GMUCERG/fobos/docs/source/examples/index.rst

****
Example Jupyter Notebooks
****

  * Correlation Power Analysis with FOBOS Shield
  * Correlation Power Analysis with Picoscope
  * Test Vector Leakage Assessment with FOBOS Shield
