GMUCERG/fobos/docs/source/modules/index.rst

.. _modules-label:

*************
FOBOS Modules
*************
FOBOS supports two boards for FOBOS Control:

#. Digilent Pynq-Z1
#. TUL Pynq-Z2

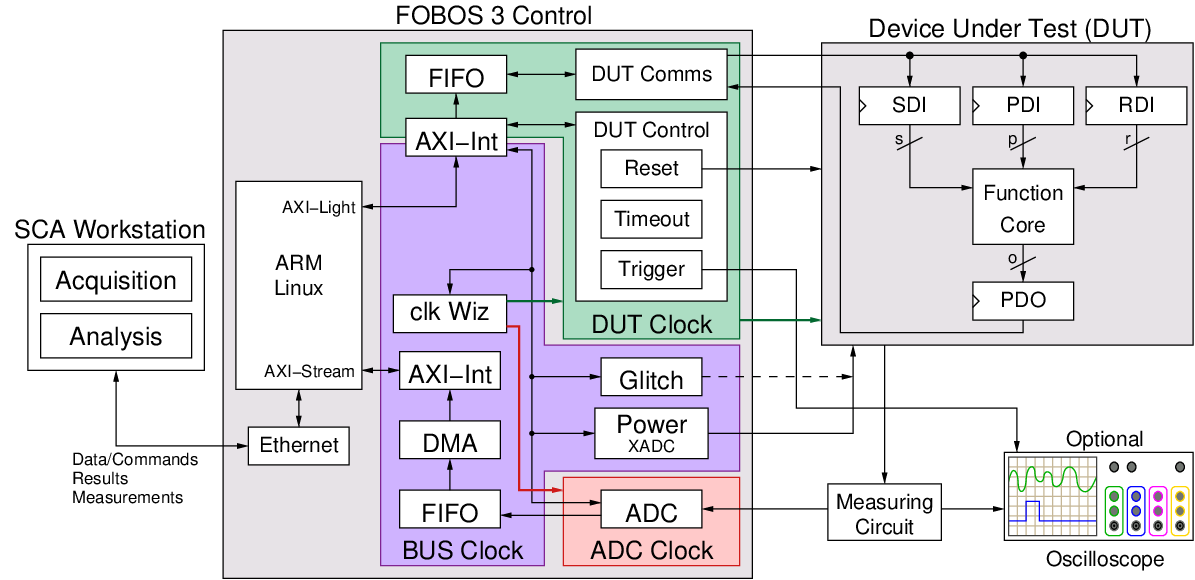
[picture p10: docs/source/figures/fobos3-block.png]


   Block Diagram of FOBOS with Pynq-Z1/Z2 as control board

Here is a list of the available modules:

- :ref:`dut_comms-label` including *DUT Interface*, *Output Length*
- :ref:`dut_control-label` including *DUT Clock*, *DUT Selection*, *Trigger*, *Reset*, *Timeout*, *Glitch*  and *DUT Working Counter*
- :ref:`openADC-label` (requires FOBOS Shield)
- :ref:`power-label` (requires FOBOS Shield)

.. toctree::
   :hidden:
   
   dut_comms
   dut_control
   openadc
   power
