GMUCERG/fobos/docs/source/teaching/index.rst

****
Class Projects
****

    * Project 1: Correlation Power Analysis (CPA) - Data Acquisition
    * Project 2: Correlation Power Analysis (CPA) - Data Analysis
    * Project 3: Side-Channel Leakage Assessment
