GMUCERG/fobos/docs/source/figures/pmod_basys3.pdf

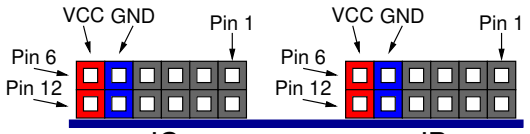
[picture p11: figure]
Pin 12; Pin 6; VCC GND; Pin 1

JC | JB
JA | JXADC
