GMUCERG/fobos/docs/source/figures/lwc/interface.pdf

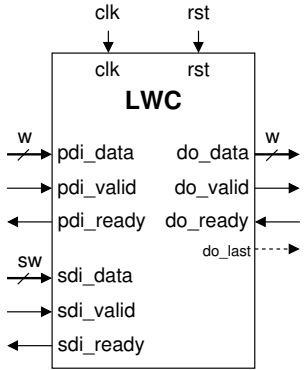
[picture p16: figure]
clk; rst; LWC; pdi_valid; pdi_ready; do_ready; do_valid; sdi_valid; sdi_ready; sdi_data; pdi_data; do_data; do_last

### Public Data Input Ports

### PDI

### Secret Data Input Ports

### SDI

### Data Output Ports

DO
