GMUCERG/fobos/docs/source/figures/lwc/interface_sca.pdf

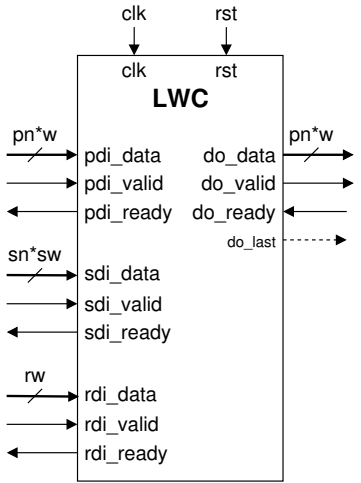
[picture p17: figure]
LWC; rdi_data; sdi_data; sdi_valid; sdi_ready; pdi_ready; pdi_valid; pdi_data; rdi_valid; rdi_ready; do_data; do_valid; do_ready; do_last; clk; rst

### PDI Public Data Input Ports

### SDI Secret Data Input Ports

### RDI Random Data Input Ports

### Data Output Ports

DO
