GMUCERG/fobos/control/pynqctrl/figures/pynq-modifications-shield-rev1.jpg

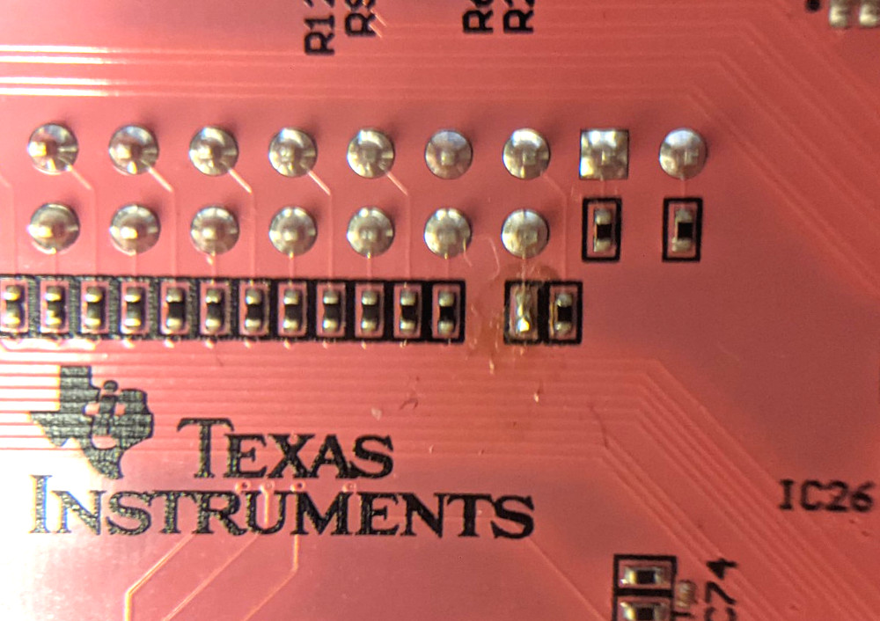
control/pynqctrl/figures/pynq-modifications-shield-rev1.jpg
