GMUCERG/fobos/control/pynqctrl/figures/resistor-R76.jpg

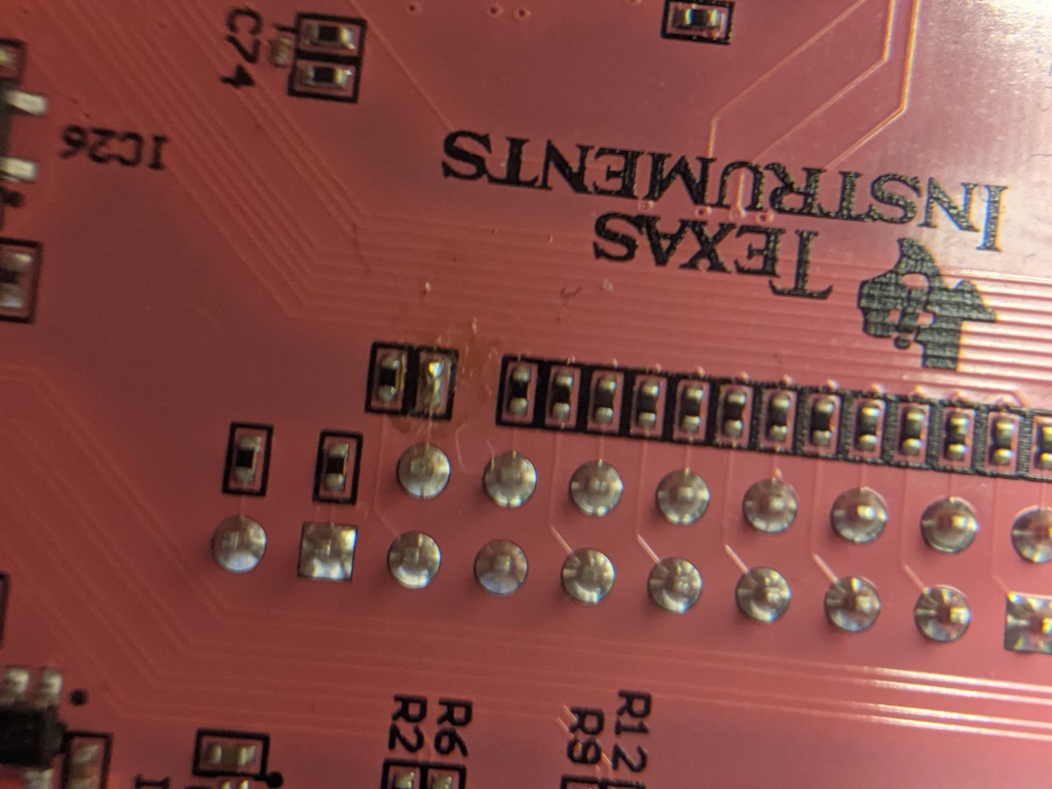
control/pynqctrl/figures/resistor-R76.jpg
