GMUCERG/fobos/docs/source/cergimg/cerg.png

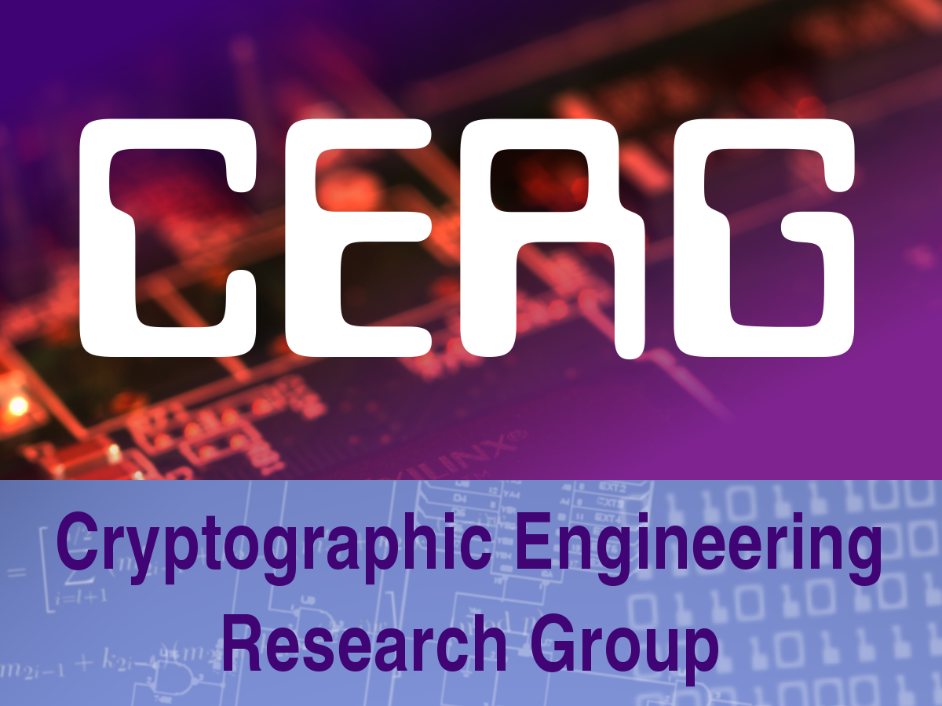
docs/source/cergimg/cerg.png
