GMUCERG/fobos/docs/source/figures/FOBOS3-Artix7-A12.jpg

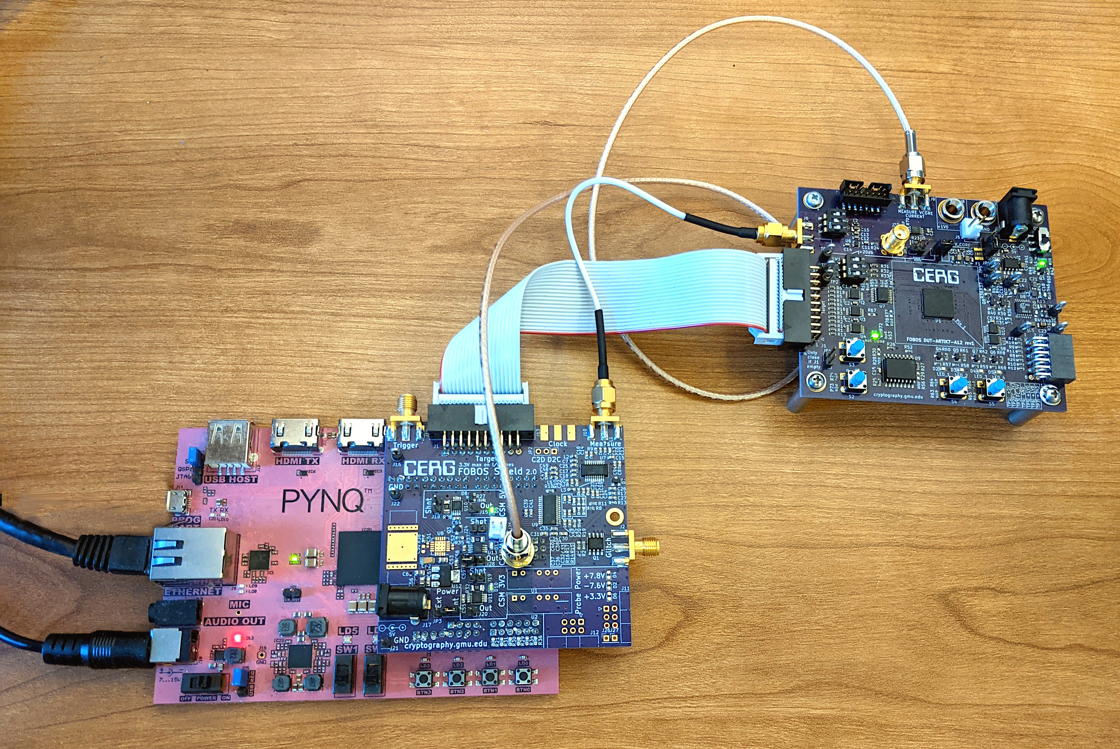
docs/source/figures/FOBOS3-Artix7-A12.jpg
