GMUCERG/fobos/docs/source/figures/FOBOS_MTC.jpg

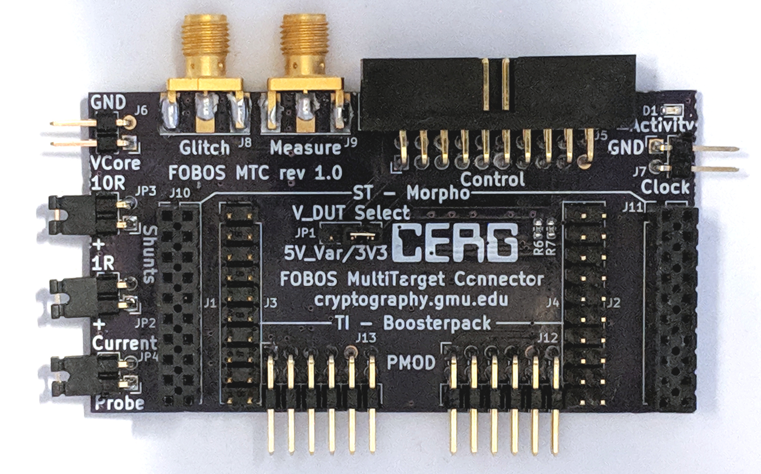
docs/source/figures/FOBOS_MTC.jpg
