GMUCERG/fobos/docs/source/figures/pmod_basys3.png

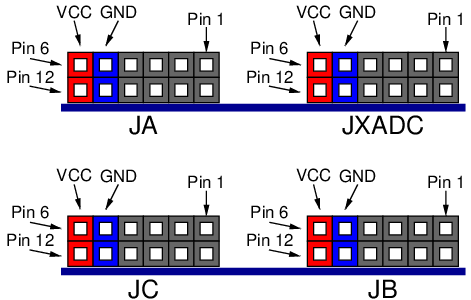
docs/source/figures/pmod_basys3.png
