GMUCERG/fobos/docs/source/figures/pmod_pynq.png

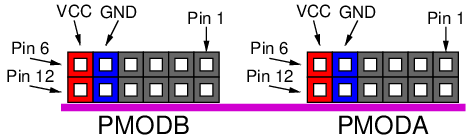
docs/source/figures/pmod_pynq.png
