GMUCERG/fobos/docs/source/figures/Pynq-Z2-modifications2.jpg

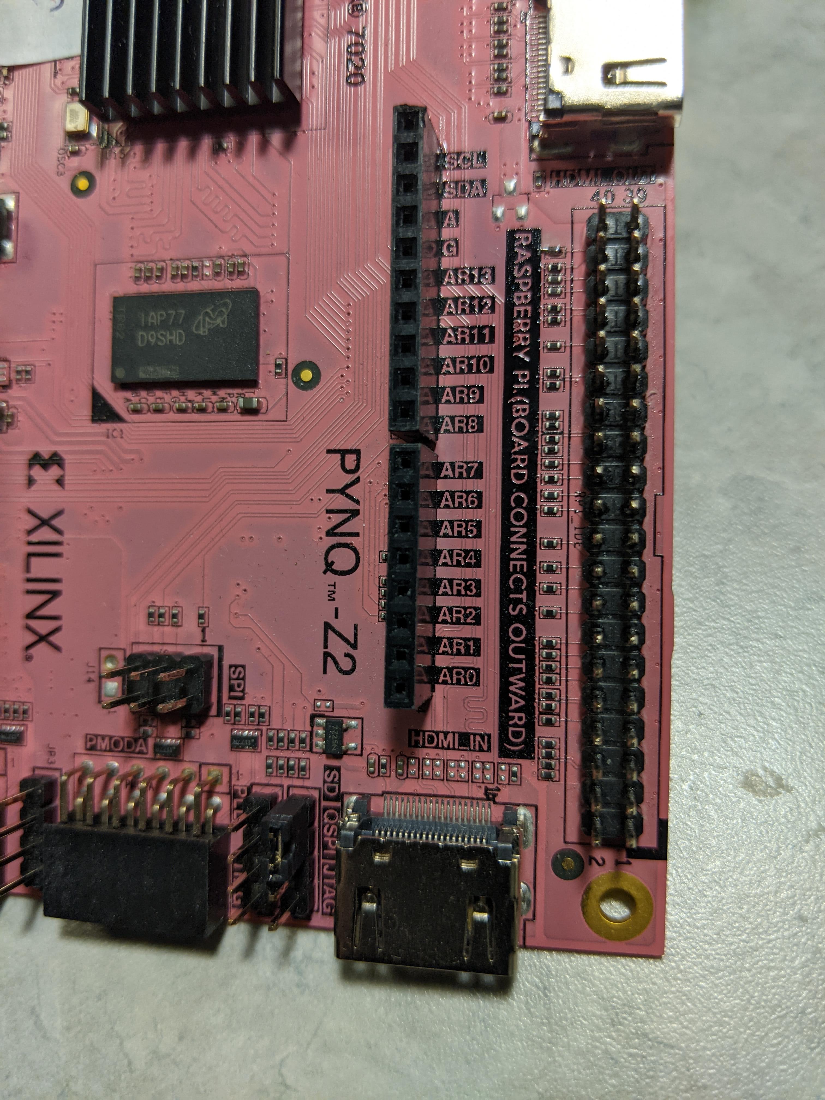
docs/source/figures/Pynq-Z2-modifications2.jpg
