GMUCERG/fobos/docs/source/figures/Pynq-Z2_with-FBD-A7.jpg

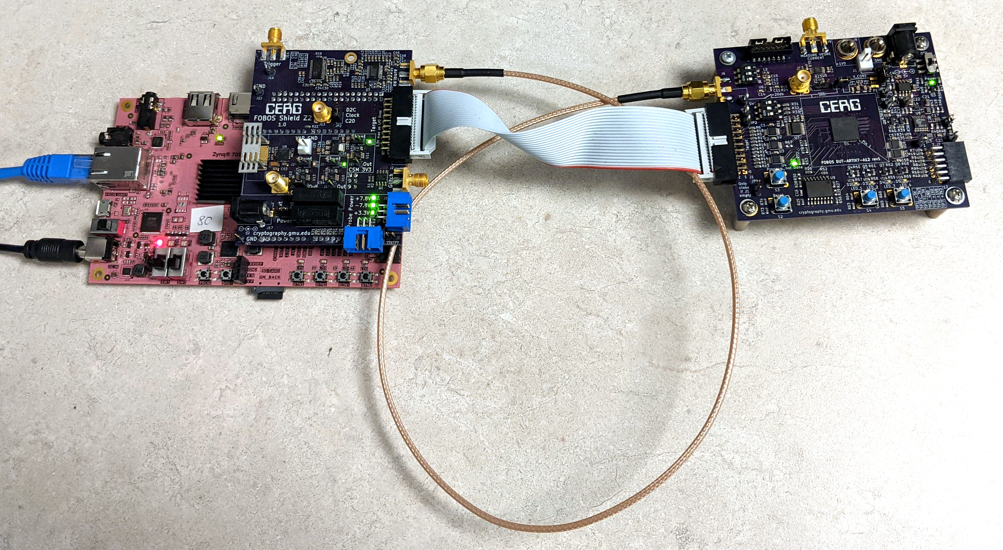
docs/source/figures/Pynq-Z2_with-FBD-A7.jpg
