GMUCERG/fobos/hardware/fobos-dut/dut-artix7-a12t-cpg238/cerg_3d_models/User Library-SSOP16.step

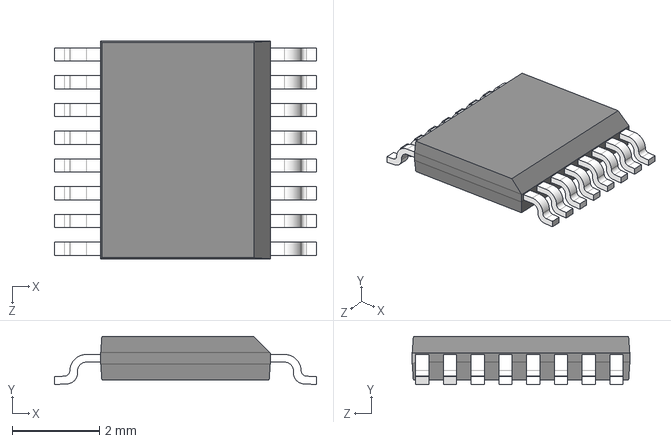
[picture p41: CAD file, 2023-11-30]
hardware/fobos-dut/dut-artix7-a12t-cpg238/cerg_3d_models/User Library-SSOP16.step
5.99 x 1.10 x 4.98 mm
