GMUCERG/fobos/hardware/fobos-dut/dut-artix7-a12t-cpg238/3d models/keystone-PN5281.STEP

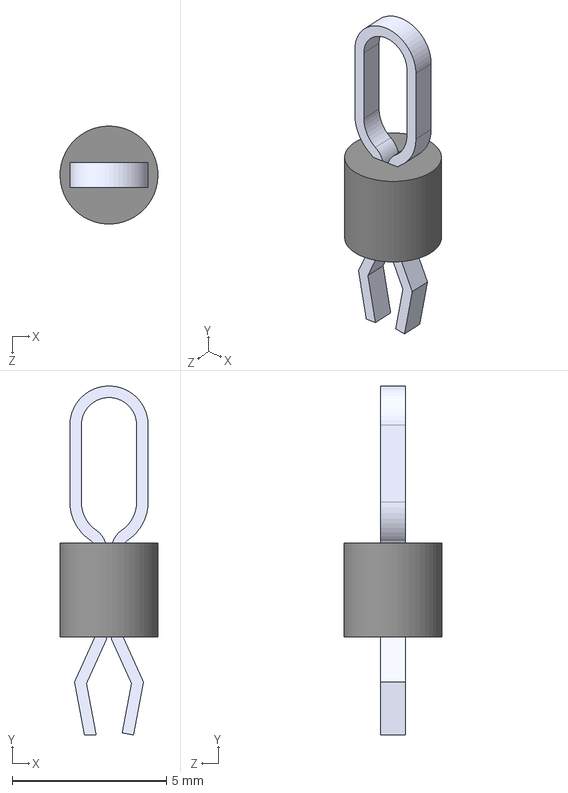
[picture p42: CAD file, 2023-11-30]
hardware/fobos-dut/dut-artix7-a12t-cpg238/3d models/keystone-PN5281.STEP
3.17 x 11.3 x 3.17 mm
