GMUCERG/fobos/hardware/fobos-dut/dut-artix7-a12t-cpg238/3d models/BRC2012T3R3MD.STEP

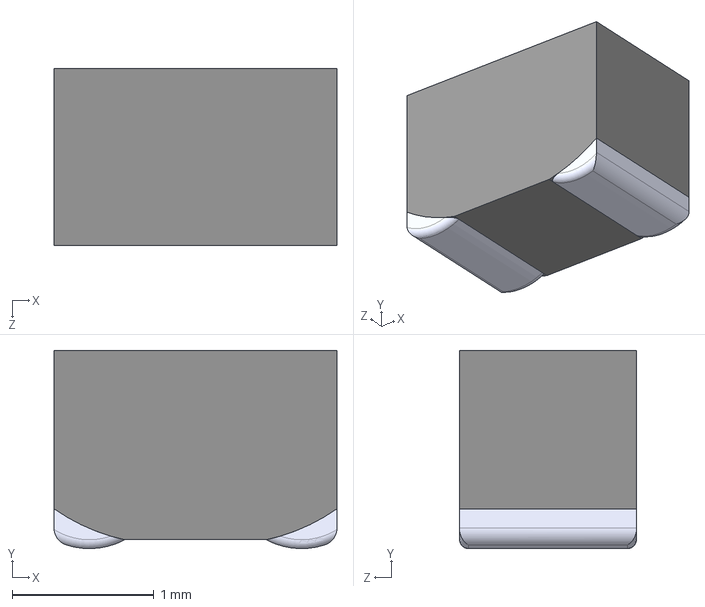
[picture p43: CAD file, 2023-11-30]
hardware/fobos-dut/dut-artix7-a12t-cpg238/3d models/BRC2012T3R3MD.STEP
2.00 x 1.40 x 1.25 mm
