GMUCERG/fobos/hardware/fobos-dut/dut-artix7-a12t-cpg238/3d models/keystone-PN575-8.STEP

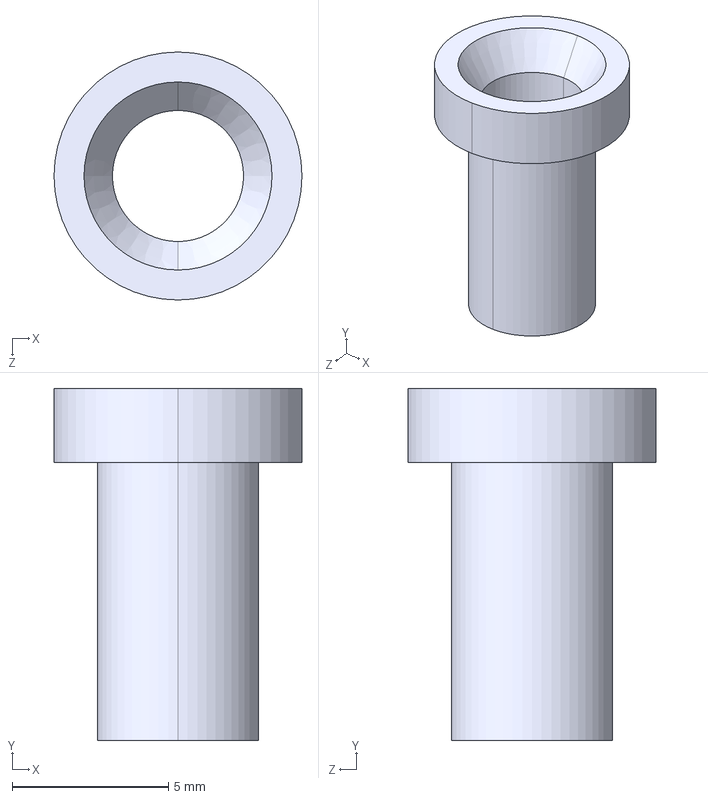
[picture p44: CAD file, 2023-11-30]
hardware/fobos-dut/dut-artix7-a12t-cpg238/3d models/keystone-PN575-8.STEP
7.92 x 11.3 x 7.92 mm
