GMUCERG/fobos/hardware/fobos-dut/dut-artix7-a12t-cpg238/3d models/XA7A25T-1CPG238Q.stp

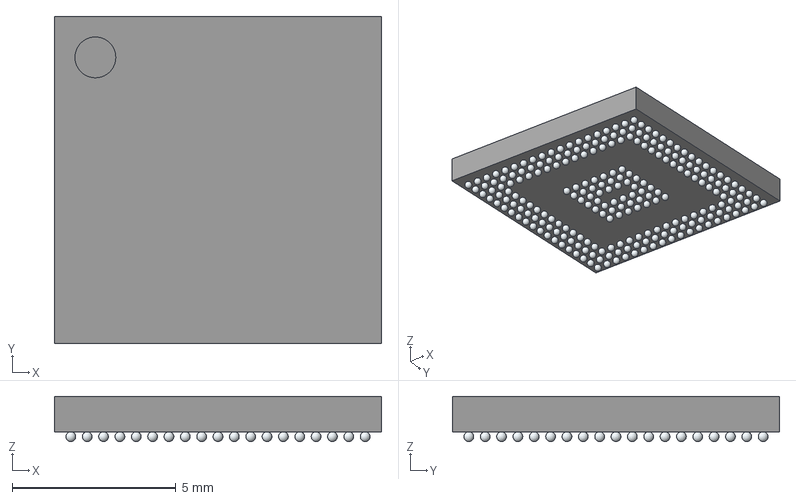
[picture p45: CAD file, 2023-11-30]
hardware/fobos-dut/dut-artix7-a12t-cpg238/3d models/XA7A25T-1CPG238Q.stp
10.0 x 10.0 x 1.38 mm
A1
A2
A3
A4
A5
A6
A7
A8
A9
A10
A11
A12
A13
A14
A15
A16
A17
A18
A19
B1
B2
B3
B4
B5
B6
B7
B8
B9
B10
B11
B12
B13
B14
B15
B16
B17
B18
B19
C1
C2
C3
C4
C5
C6
C7
C8
C9
C10
C11
C12
C13
C14
C15
C16
C17
C18
C19
D1
D2
D3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
