GMUCERG/fobos/software/notebooks/sca_labs/figures/FOBOS3-lab-setup.jpg

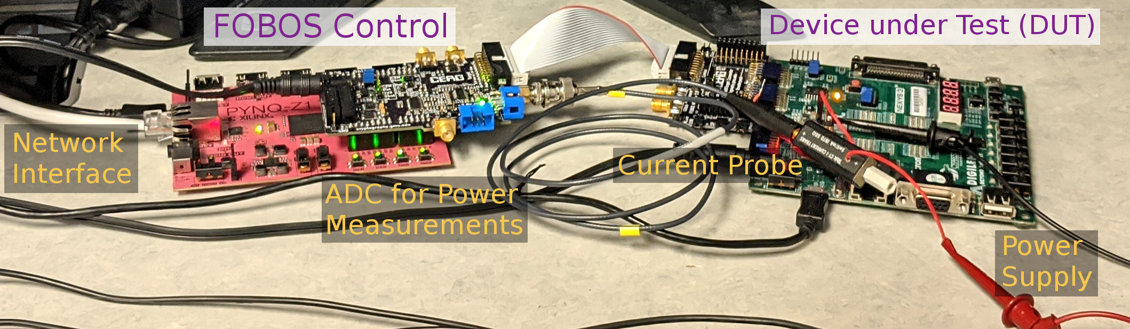
software/notebooks/sca_labs/figures/FOBOS3-lab-setup.jpg
