GMUCERG/fobos/control/ip_repo/dut_controller_1.0/drivers/dut_controller_v1_0/src/dut_controller.h

#ifndef DUT_CONTROLLER_H
#define DUT_CONTROLLER_H


/****************** Include Files ********************/
#include "xil_types.h"
#include "xstatus.h"

#define DUT_CONTROLLER_S_AXI_SLV_REG0_OFFSET 0
#define DUT_CONTROLLER_S_AXI_SLV_REG1_OFFSET 4
#define DUT_CONTROLLER_S_AXI_SLV_REG2_OFFSET 8
#define DUT_CONTROLLER_S_AXI_SLV_REG3_OFFSET 12
#define DUT_CONTROLLER_S_AXI_SLV_REG4_OFFSET 16
#define DUT_CONTROLLER_S_AXI_SLV_REG5_OFFSET 20
#define DUT_CONTROLLER_S_AXI_SLV_REG6_OFFSET 24
#define DUT_CONTROLLER_S_AXI_SLV_REG7_OFFSET 28


/**************************** Type Definitions *****************************/
/**
 *
 * Write a value to a DUT_CONTROLLER register. A 32 bit write is performed.
 * If the component is implemented in a smaller width, only the least
 * significant data is written.
 *
 * @param   BaseAddress is the base address of the DUT_CONTROLLERdevice.
 * @param   RegOffset is the register offset from the base to write to.
 * @param   Data is the data written to the register.
 *
 * @return  None.
 *
 * @note
 * C-style signature:
 * 	void DUT_CONTROLLER_mWriteReg(u32 BaseAddress, unsigned RegOffset, u32 Data)
 *
 */
#define DUT_CONTROLLER_mWriteReg(BaseAddress, RegOffset, Data) \
  	Xil_Out32((BaseAddress) + (RegOffset), (u32)(Data))

/**
 *
 * Read a value from a DUT_CONTROLLER register. A 32 bit read is performed.
 * If the component is implemented in a smaller width, only the least
 * significant data is read from the register. The most significant data
 * will be read as 0.
 *
 * @param   BaseAddress is the base address of the DUT_CONTROLLER device.
 * @param   RegOffset is the register offset from the base to write to.
 *
 * @return  Data is the data from the register.
 *
 * @note
 * C-style signature:
 * 	u32 DUT_CONTROLLER_mReadReg(u32 BaseAddress, unsigned RegOffset)
 *
 */
#define DUT_CONTROLLER_mReadReg(BaseAddress, RegOffset) \
    Xil_In32((BaseAddress) + (RegOffset))

/************************** Function Prototypes ****************************/
/**
 *
 * Run a self-test on the driver/device. Note this may be a destructive test if
 * resets of the device are performed.
 *
 * If the hardware system is not built correctly, this function may never
 * return to the caller.
 *
 * @param   baseaddr_p is the base address of the DUT_CONTROLLER instance to be worked on.
 *
 * @return
 *
 *    - XST_SUCCESS   if all self-test code passed
 *    - XST_FAILURE   if any self-test code failed
 *
 * @note    Caching must be turned off for this function to work.
 * @note    Self test may fail if data memory and device are not on the same bus.
 *
 */
XStatus DUT_CONTROLLER_Reg_SelfTest(void * baseaddr_p);

#endif // DUT_CONTROLLER_H
