GMUCERG/fobos/control/ip_repo/powermanager_1.1/src/xadc_wiz_0/xadc_wiz_0.vhd

-- file: xadc_wiz_0.vhd
-- (c) Copyright 2009 - 2013 Xilinx, Inc. All rights reserved.
-- 
-- This file contains confidential and proprietary information
-- of Xilinx, Inc. and is protected under U.S. and
-- international copyright and other intellectual property
-- laws.
-- 
-- DISCLAIMER
-- This disclaimer is not a license and does not grant any
-- rights to the materials distributed herewith. Except as
-- otherwise provided in a valid license issued to you by
-- Xilinx, and to the maximum extent permitted by applicable
-- law: (1) THESE MATERIALS ARE MADE AVAILABLE "AS IS" AND
-- WITH ALL FAULTS, AND XILINX HEREBY DISCLAIMS ALL WARRANTIES
-- AND CONDITIONS, EXPRESS, IMPLIED, OR STATUTORY, INCLUDING
-- BUT NOT LIMITED TO WARRANTIES OF MERCHANTABILITY, NON-
-- INFRINGEMENT, OR FITNESS FOR ANY PARTICULAR PURPOSE; and
-- (2) Xilinx shall not be liable (whether in contract or tort,
-- including negligence, or under any other theory of
-- liability) for any loss or damage of any kind or nature
-- related to, arising under or in connection with these
-- materials, including for any direct, or any indirect,
-- special, incidental, or consequential loss or damage
-- (including loss of data, profits, goodwill, or any type of
-- loss or damage suffered as a result of any action brought
-- by a third party) even if such damage or loss was
-- reasonably foreseeable or Xilinx had been advised of the
-- possibility of the same.
-- 
-- CRITICAL APPLICATIONS
-- Xilinx products are not designed or intended to be fail-
-- safe, or for use in any application requiring fail-safe
-- performance, such as life-support or safety devices or
-- systems, Class III medical devices, nuclear facilities,
-- applications related to the deployment of airbags, or any
-- other applications that could lead to death, personal
-- injury, or severe property or environmental damage
-- (individually and collectively, "Critical
-- Applications"). Customer assumes the sole risk and
-- liability of any use of Xilinx products in Critical
-- Applications, subject only to applicable laws and
-- regulations governing limitations on product liability.
-- 
-- THIS COPYRIGHT NOTICE AND DISCLAIMER MUST BE RETAINED AS
-- PART OF THIS FILE AT ALL TIMES.

library ieee;
use ieee.std_logic_1164.all;
use ieee.numeric_std.all;
Library UNISIM;
use UNISIM.VCOMPONENTS.ALL;

entity xadc_wiz_0 is
   port
   (
    daddr_in        : in  STD_LOGIC_VECTOR (6 downto 0);     -- Address bus for the dynamic reconfiguration port
    den_in          : in  STD_LOGIC;                         -- Enable Signal for the dynamic reconfiguration port
    di_in           : in  STD_LOGIC_VECTOR (15 downto 0);    -- Input data bus for the dynamic reconfiguration port
    dwe_in          : in  STD_LOGIC;                         -- Write Enable for the dynamic reconfiguration port
    do_out          : out  STD_LOGIC_VECTOR (15 downto 0);   -- Output data bus for dynamic reconfiguration port
    drdy_out        : out  STD_LOGIC;                        -- Data ready signal for the dynamic reconfiguration port
    dclk_in         : in  STD_LOGIC;                         -- Clock input for the dynamic reconfiguration port
    reset_in        : in  STD_LOGIC;                         -- Reset signal for the System Monitor control logic
    vauxp1          : in  STD_LOGIC;                         -- Auxiliary Channel 1
    vauxn1          : in  STD_LOGIC;
    vauxp5          : in  STD_LOGIC;                         -- Auxiliary Channel 5
    vauxn5          : in  STD_LOGIC;
    vauxp6          : in  STD_LOGIC;                         -- Auxiliary Channel 6
    vauxn6          : in  STD_LOGIC;
    vauxp9          : in  STD_LOGIC;                         -- Auxiliary Channel 9
    vauxn9          : in  STD_LOGIC;
    vauxp13         : in  STD_LOGIC;                         -- Auxiliary Channel 13
    vauxn13         : in  STD_LOGIC;
    vauxp15         : in  STD_LOGIC;                         -- Auxiliary Channel 15
    vauxn15         : in  STD_LOGIC;
    busy_out        : out  STD_LOGIC;                        -- ADC Busy signal
    channel_out     : out  STD_LOGIC_VECTOR (4 downto 0);    -- Channel Selection Outputs
    eoc_out         : out  STD_LOGIC;                        -- End of Conversion Signal
    eos_out         : out  STD_LOGIC;                        -- End of Sequence Signal
    alarm_out       : out STD_LOGIC;                         -- OR'ed output of all the Alarms
    vp_in           : in  STD_LOGIC;                         -- Dedicated Analog Input Pair
    vn_in           : in  STD_LOGIC
);
end xadc_wiz_0;

architecture xilinx of xadc_wiz_0 is

  attribute CORE_GENERATION_INFO : string;
  attribute CORE_GENERATION_INFO of xilinx : architecture is "xadc_wiz_0,xadc_wiz_v3_3_8,{component_name=xadc_wiz_0,enable_axi=false,enable_axi4stream=false,dclk_frequency=100,enable_busy=true,enable_convst=false,enable_convstclk=false,enable_dclk=true,enable_drp=true,enable_eoc=true,enable_eos=true,enable_vbram_alaram=false,enable_vccddro_alaram=false,enable_Vccint_Alaram=false,enable_Vccaux_alaram=falseenable_vccpaux_alaram=false,enable_vccpint_alaram=false,ot_alaram=false,user_temp_alaram=false,timing_mode=continuous,channel_averaging=None,sequencer_mode=on,startup_channel_selection=contineous_sequence}";


  signal FLOAT_VCCAUX_ALARM : std_logic;
  signal FLOAT_VCCINT_ALARM : std_logic;
  signal FLOAT_USER_TEMP_ALARM : std_logic;
  signal FLOAT_VBRAM_ALARM : std_logic;
  signal FLOAT_MUXADDR : std_logic_vector (4 downto 0);
  signal aux_channel_p : std_logic_vector (15 downto 0);
  signal aux_channel_n : std_logic_vector (15 downto 0);
  signal alm_int : std_logic_vector (7 downto 0);

begin

       alarm_out <= alm_int(7);

        aux_channel_p(0) <= '0';
        aux_channel_n(0) <= '0';

        aux_channel_p(1) <= vauxp1;
        aux_channel_n(1) <= vauxn1;

        aux_channel_p(2) <= '0';
        aux_channel_n(2) <= '0';

        aux_channel_p(3) <= '0';
        aux_channel_n(3) <= '0';

        aux_channel_p(4) <= '0';
        aux_channel_n(4) <= '0';

        aux_channel_p(5) <= vauxp5;
        aux_channel_n(5) <= vauxn5;

        aux_channel_p(6) <= vauxp6;
        aux_channel_n(6) <= vauxn6;

        aux_channel_p(7) <= '0';
        aux_channel_n(7) <= '0';

        aux_channel_p(8) <= '0';
        aux_channel_n(8) <= '0';

        aux_channel_p(9) <= vauxp9;
        aux_channel_n(9) <= vauxn9;

        aux_channel_p(10) <= '0';
        aux_channel_n(10) <= '0';

        aux_channel_p(11) <= '0';
        aux_channel_n(11) <= '0';

        aux_channel_p(12) <= '0';
        aux_channel_n(12) <= '0';

        aux_channel_p(13) <= vauxp13;
        aux_channel_n(13) <= vauxn13;

        aux_channel_p(14) <= '0';
        aux_channel_n(14) <= '0';

        aux_channel_p(15) <= vauxp15;
        aux_channel_n(15) <= vauxn15;

 U0 : XADC
     generic map(
        INIT_40 => X"0000", -- config reg 0
        INIT_41 => X"21AF", -- config reg 1
        INIT_42 => X"0400", -- config reg 2
        INIT_48 => X"0800", -- Sequencer channel selection
        INIT_49 => X"A262", -- Sequencer channel selection
        INIT_4A => X"0000", -- Sequencer Average selection
        INIT_4B => X"0000", -- Sequencer Average selection
        INIT_4C => X"0000", -- Sequencer Bipolar selection
        INIT_4D => X"0000", -- Sequencer Bipolar selection
        INIT_4E => X"0000", -- Sequencer Acq time selection
        INIT_4F => X"0000", -- Sequencer Acq time selection
        INIT_50 => X"B5ED", -- Temp alarm trigger
        INIT_51 => X"57E4", -- Vccint upper alarm limit
        INIT_52 => X"A147", -- Vccaux upper alarm limit
        INIT_53 => X"CA33",  -- Temp alarm OT upper
        INIT_54 => X"A93A", -- Temp alarm reset
        INIT_55 => X"52C6", -- Vccint lower alarm limit
        INIT_56 => X"9555", -- Vccaux lower alarm limit
        INIT_57 => X"AE4E",  -- Temp alarm OT reset
        INIT_58 => X"5999",  -- Vccbram upper alarm limit
        INIT_5C => X"5111",  -- Vccbram lower alarm limit
        INIT_59 => X"5555",  -- Vccpint upper alarm limit
        INIT_5D => X"5111",  -- Vccpint lower alarm limit
        INIT_5A => X"9999",  -- Vccpaux upper alarm limit
        INIT_5E => X"91EB",  -- Vccpaux lower alarm limit
        INIT_5B => X"6AAA",  -- Vccddro upper alarm limit
        INIT_5F => X"6666",  -- Vccddro lower alarm limit
        SIM_DEVICE => "ZYNQ",
        SIM_MONITOR_FILE => "design.txt"
        )

port map (
        CONVST              => '0',
        CONVSTCLK           => '0',
        DADDR(6 downto 0)   => daddr_in(6 downto 0),
        DCLK                => dclk_in,
        DEN                 => den_in,
        DI(15 downto 0)     => di_in(15 downto 0),
        DWE                 => dwe_in,
        RESET               => reset_in,
        VAUXN(15 downto 0)  => aux_channel_n(15 downto 0),
        VAUXP(15 downto 0)  => aux_channel_p(15 downto 0),
        ALM                 => alm_int,
        BUSY                => busy_out,
        CHANNEL(4 downto 0) => channel_out(4 downto 0),
        DO(15 downto 0)     => do_out(15 downto 0),
        DRDY                => drdy_out,
        EOC                 => eoc_out,
        EOS                 => eos_out,
        JTAGBUSY            => open,
        JTAGLOCKED          => open,
        JTAGMODIFIED        => open,
        OT                  => open,
     
        MUXADDR             => FLOAT_MUXADDR,
        VN                  => vn_in,
        VP                  => vp_in
         );
end xilinx;
