GMUCERG/fobos/control/ip_repo/openadc_1.0/hdl/openadc_v1_0_M_AXIS.vhd

--#############################################################################
--#                                                                           #
--#   Copyright 2018-2023 Cryptographic Engineering Research Group (CERG)     #
--#                                                                           #
--#   Licensed under the Apache License, Version 2.0 (the "License");         #
--#   you may not use this file except in compliance with the License.        #
--#   You may obtain a copy of the License at                                 #
--#                                                                           #
--#       http://www.apache.org/licenses/LICENSE-2.0                          #
--#                                                                           #
--#   Unless required by applicable law or agreed to in writing, software     #
--#   distributed under the License is distributed on an "AS IS" BASIS,       #
--#   WITHOUT WARRANTIES OR CONDITIONS OF ANY KIND, either express or implied.#
--#   See the License for the specific language governing permissions and     #
--#   limitations under the License.                                          #
--#                                                                           #
--#############################################################################

----------------------------------------------------------------------------------
-- Company: Cryptographic Engineering Research Group (CERG)
-- ECE Department, George Mason University
--     Fairfax, VA, U.S.A.
--     URL: http://cryptography.gmu.edu
-- Author: Matthew Carter

library ieee;
use ieee.std_logic_1164.all;
use ieee.numeric_std.all;

entity openadc_v1_0_M_AXIS is
	generic (
		-- Users to add parameters here

		-- User parameters ends
		-- Do not modify the parameters beyond this line

		-- Width of S_AXIS address bus. The slave accepts the read and write addresses of width C_M_AXIS_TDATA_WIDTH.
		C_M_AXIS_TDATA_WIDTH	: integer	:= 64;
		-- Start count is the numeber of clock cycles the master will wait before initiating/issuing any transaction.
		C_M_START_COUNT	: integer	:= 32
	);
	port (
		-- Users to add ports here
        START_TRANSMIT : in std_logic;
        ADC_DATA : in std_logic_vector(C_M_AXIS_TDATA_WIDTH-1 downto 0);
        TRANSMIT_DONE : out std_logic;
        BLOCK_SIZE_CONF : in std_logic_vector(9 downto 0);
        RESET_TRANSMIT : in std_logic;
		-- User ports ends
		-- Do not modify the ports beyond this line

		-- Global ports
		M_AXIS_ACLK	: in std_logic;
		-- 
		M_AXIS_ARESETN	: in std_logic;
		-- Master Stream Ports. TVALID indicates that the master is driving a valid transfer, A transfer takes place when both TVALID and TREADY are asserted. 
		M_AXIS_TVALID	: out std_logic;
		-- TDATA is the primary payload that is used to provide the data that is passing across the interface from the master.
		M_AXIS_TDATA	: out std_logic_vector(C_M_AXIS_TDATA_WIDTH-1 downto 0);
		-- TSTRB is the byte qualifier that indicates whether the content of the associated byte of TDATA is processed as a data byte or a position byte.
		M_AXIS_TSTRB	: out std_logic_vector((C_M_AXIS_TDATA_WIDTH/8)-1 downto 0);
		-- TLAST indicates the boundary of a packet.
		M_AXIS_TLAST	: out std_logic;
		-- TREADY indicates that the slave can accept a transfer in the current cycle.
		M_AXIS_TREADY	: in std_logic
	);
end openadc_v1_0_M_AXIS;

architecture implementation of openadc_v1_0_M_AXIS is
	--Total number of output data.
	-- Total number of output data                                              
	constant NUMBER_OF_OUTPUT_WORDS : integer := 1;                                                                                                 
	                                                                                  
	-- In this example, Depth of FIFO is determined by the greater of                 
	-- the number of input words and output words.                                    
	constant depth : integer := NUMBER_OF_OUTPUT_WORDS;
	constant max_block_size : integer := 1024;                               
	                                                                                  
	                                                                                  
	-- Define the states of state machine                                             
	-- The control state machine oversees the writing of input streaming data to the FIFO,
	-- and outputs the streaming data from the FIFO                                   
	type state is ( IDLE,        -- This is the initial/idle state                    
	                SEND_STREAM);  -- In this state the                               
	                             -- stream data is output through M_AXIS_TDATA      
	signal block_size : integer range 0 to max_block_size;  
	-- State variable                                                                 
	signal  mst_exec_state : state;                                                   
	-- Example design FIFO read pointer                                               
	signal transfer_count : integer range 0 to max_block_size;                               

	-- AXI Stream internal signals
	--streaming data valid
	signal axis_tvalid	: std_logic;
	--streaming data valid delayed by one clock cycle
	signal axis_tvalid_delay	: std_logic;
	--Last of the streaming data 
	signal axis_tlast	: std_logic;
	--Last of the streaming data delayed by one clock cycle
	signal axis_tlast_delay	: std_logic;
	--FIFO implementation signals
	signal stream_data_out	: std_logic_vector(C_M_AXIS_TDATA_WIDTH-1 downto 0);
	signal tx_en	: std_logic;
	--The master has issued all the streaming data stored in FIFO
	signal tx_done	: std_logic;
	signal tx_sent : std_logic;
	signal stored_out : std_logic_vector(C_M_AXIS_TDATA_WIDTH-1 downto 0);


begin
	-- I/O Connections assignments

	M_AXIS_TVALID	<= axis_tvalid_delay;
	M_AXIS_TDATA	<= stream_data_out;
	M_AXIS_TLAST	<= axis_tlast_delay;
	M_AXIS_TSTRB	<= (others => '1');
    TRANSMIT_DONE <= tx_done;
    block_size <= to_integer(unsigned(BLOCK_SIZE_CONF));

	-- Control state machine implementation                                               
	process(M_AXIS_ACLK)                                                                        
	begin                                                                                       
	  if (rising_edge (M_AXIS_ACLK)) then                                                       
	    if(M_AXIS_ARESETN = '0') then                                                           
	      -- Synchronous reset (active low)                                                     
	      mst_exec_state      <= IDLE;                                                          
	      transfer_count <= 0;
	    elsif (RESET_TRANSMIT = '1') then
	      mst_exec_state      <= IDLE;                                                          
          transfer_count <= 0;                                                             
	    else                                                                                    
	      case (mst_exec_state) is                                                              
	        when IDLE     =>                                                                    
	          -- The slave starts accepting tdata when                                          
	          -- there tvalid is asserted to mark the                                           
	          -- presence of valid streaming data                                               
	          --if (count = "0")then
	          if(START_TRANSMIT = '1' and tx_en = '1') then    
	            --read_pointer <= 0;                                                      
	            mst_exec_state <= SEND_STREAM;
	            stored_out <= ADC_DATA;
	            transfer_count <= transfer_count + 1;
	          end if;                                                 
	          --else                                                                              
	          --  mst_exec_state <= IDLE;                                                         
	          --end if;                                                                                                                                                 
	                                                                                            
	        when SEND_STREAM  =>                                                                
	          -- The example design streaming master functionality starts                       
	          -- when the master drives output tdata from the FIFO and the slave                
	          -- has finished storing the S_AXIS_TDATA                                          
	          if (tx_sent = '1') then
	            if (transfer_count = block_size) then
	                transfer_count <= 0;
	            end if;                                                           
	            mst_exec_state <= IDLE;
	          else                                                                              
	            mst_exec_state <= SEND_STREAM;                                                  
	          end if;                                                                           
	                                                                                            
	        when others    =>                                                                   
	          mst_exec_state <= IDLE;                                                           
	                                                                                            
	      end case;                                                                             
	    end if;                                                                                 
	  end if;                                                                                   
	end process;                                                                                


	--tvalid generation
	--axis_tvalid is asserted when the control state machine's state is SEND_STREAM and
	--number of output streaming data is less than the NUMBER_OF_OUTPUT_WORDS.
	axis_tvalid <= '1' when (mst_exec_state = SEND_STREAM) else '0';
	                                                                                               
	-- AXI tlast generation                                                                        
	-- axis_tlast is asserted number of output streaming data is NUMBER_OF_OUTPUT_WORDS-1          
	-- (0 to NUMBER_OF_OUTPUT_WORDS-1)                                                             
	axis_tlast <= '1' when ((mst_exec_state = SEND_STREAM) and (transfer_count = block_size)) else '0';
	
	tx_done <= '1' when (mst_exec_state = SEND_STREAM) else '0';                
	                                                                                               
	-- Delay the axis_tvalid and axis_tlast signal by one clock cycle                              
	-- to match the latency of M_AXIS_TDATA                                                        
	process(M_AXIS_ACLK)                                                                           
	begin                                                                                          
	  if (rising_edge (M_AXIS_ACLK)) then                                                          
	    if(M_AXIS_ARESETN = '0') then                                                              
	      axis_tvalid_delay <= '0';                                                                
	      axis_tlast_delay <= '0';                                                                 
	    else                                                                                       
	      axis_tvalid_delay <= axis_tvalid;                                                        
	      axis_tlast_delay <= axis_tlast;                                                          
	    end if;                                                                                    
	  end if;                                                                                      
	end process;                                                                                                                                                        


	tx_en <= M_AXIS_TREADY;                                   
	                                                                                	                                                                                
	  process(M_AXIS_ACLK)                                                          
	  variable  sig_one : integer := 1;                                             
	  begin                                                                         
	    if (rising_edge (M_AXIS_ACLK)) then                                         
	      if(M_AXIS_ARESETN = '0') then                                             
	    	stream_data_out <= std_logic_vector(to_unsigned(sig_one,C_M_AXIS_TDATA_WIDTH)); 
	    	tx_sent <= '0';
	      elsif (tx_en = '1') then -- && M_AXIS_TSTRB(byte_index)                   
	        stream_data_out <= stored_out;
	        tx_sent <= '1';
	      else
	        stream_data_out <= (others => '0');
	        tx_sent <= '0';
	      end if;                                                                   
	     end if;                                                                    
	   end process;                                                                 

end implementation;
