GMUCERG/fobos/control/ip_repo/powermanager_1.1/src/xadc_wiz_0/xadc_wiz_0_sim_netlist.vhdl

-- Copyright 1986-2020 Xilinx, Inc. All Rights Reserved.
-- --------------------------------------------------------------------------------
-- Tool Version: Vivado v.2020.2 (lin64) Build 3064766 Wed Nov 18 09:12:47 MST 2020
-- Date        : Fri Jul  2 18:59:17 2021
-- Host        : goedel running 64-bit Ubuntu 20.04.2 LTS
-- Command     : write_vhdl -force -mode funcsim
--               /home/jkaps/projects/FOBOS/fobos3/control/ip_repo/powermanager_1.1/src/xadc_wiz_0/xadc_wiz_0_sim_netlist.vhdl
-- Design      : xadc_wiz_0
-- Purpose     : This VHDL netlist is a functional simulation representation of the design and should not be modified or
--               synthesized. This netlist cannot be used for SDF annotated simulation.
-- Device      : xc7z020clg400-1
-- --------------------------------------------------------------------------------
library IEEE;
use IEEE.STD_LOGIC_1164.ALL;
library UNISIM;
use UNISIM.VCOMPONENTS.ALL;
entity xadc_wiz_0 is
  port (
    daddr_in : in STD_LOGIC_VECTOR ( 6 downto 0 );
    den_in : in STD_LOGIC;
    di_in : in STD_LOGIC_VECTOR ( 15 downto 0 );
    dwe_in : in STD_LOGIC;
    do_out : out STD_LOGIC_VECTOR ( 15 downto 0 );
    drdy_out : out STD_LOGIC;
    dclk_in : in STD_LOGIC;
    reset_in : in STD_LOGIC;
    vauxp1 : in STD_LOGIC;
    vauxn1 : in STD_LOGIC;
    vauxp5 : in STD_LOGIC;
    vauxn5 : in STD_LOGIC;
    vauxp6 : in STD_LOGIC;
    vauxn6 : in STD_LOGIC;
    vauxp9 : in STD_LOGIC;
    vauxn9 : in STD_LOGIC;
    vauxp13 : in STD_LOGIC;
    vauxn13 : in STD_LOGIC;
    vauxp15 : in STD_LOGIC;
    vauxn15 : in STD_LOGIC;
    busy_out : out STD_LOGIC;
    channel_out : out STD_LOGIC_VECTOR ( 4 downto 0 );
    eoc_out : out STD_LOGIC;
    eos_out : out STD_LOGIC;
    alarm_out : out STD_LOGIC;
    vp_in : in STD_LOGIC;
    vn_in : in STD_LOGIC
  );
  attribute NotValidForBitStream : boolean;
  attribute NotValidForBitStream of xadc_wiz_0 : entity is true;
end xadc_wiz_0;

architecture STRUCTURE of xadc_wiz_0 is
  signal NLW_U0_JTAGBUSY_UNCONNECTED : STD_LOGIC;
  signal NLW_U0_JTAGLOCKED_UNCONNECTED : STD_LOGIC;
  signal NLW_U0_JTAGMODIFIED_UNCONNECTED : STD_LOGIC;
  signal NLW_U0_OT_UNCONNECTED : STD_LOGIC;
  signal NLW_U0_ALM_UNCONNECTED : STD_LOGIC_VECTOR ( 6 downto 0 );
  signal NLW_U0_MUXADDR_UNCONNECTED : STD_LOGIC_VECTOR ( 4 downto 0 );
  attribute box_type : string;
  attribute box_type of U0 : label is "PRIMITIVE";
begin
U0: unisim.vcomponents.XADC
    generic map(
      INIT_40 => X"0000",
      INIT_41 => X"21AF",
      INIT_42 => X"0400",
      INIT_43 => X"0000",
      INIT_44 => X"0000",
      INIT_45 => X"0000",
      INIT_46 => X"0000",
      INIT_47 => X"0000",
      INIT_48 => X"0800",
      INIT_49 => X"A262",
      INIT_4A => X"0000",
      INIT_4B => X"0000",
      INIT_4C => X"0000",
      INIT_4D => X"0000",
      INIT_4E => X"0000",
      INIT_4F => X"0000",
      INIT_50 => X"B5ED",
      INIT_51 => X"57E4",
      INIT_52 => X"A147",
      INIT_53 => X"CA33",
      INIT_54 => X"A93A",
      INIT_55 => X"52C6",
      INIT_56 => X"9555",
      INIT_57 => X"AE4E",
      INIT_58 => X"5999",
      INIT_59 => X"5555",
      INIT_5A => X"9999",
      INIT_5B => X"6AAA",
      INIT_5C => X"5111",
      INIT_5D => X"5111",
      INIT_5E => X"91EB",
      INIT_5F => X"6666",
      IS_CONVSTCLK_INVERTED => '0',
      IS_DCLK_INVERTED => '0',
      SIM_DEVICE => "ZYNQ",
      SIM_MONITOR_FILE => "design.txt"
    )
        port map (
      ALM(7) => alarm_out,
      ALM(6 downto 0) => NLW_U0_ALM_UNCONNECTED(6 downto 0),
      BUSY => busy_out,
      CHANNEL(4 downto 0) => channel_out(4 downto 0),
      CONVST => '0',
      CONVSTCLK => '0',
      DADDR(6 downto 0) => daddr_in(6 downto 0),
      DCLK => dclk_in,
      DEN => den_in,
      DI(15 downto 0) => di_in(15 downto 0),
      DO(15 downto 0) => do_out(15 downto 0),
      DRDY => drdy_out,
      DWE => dwe_in,
      EOC => eoc_out,
      EOS => eos_out,
      JTAGBUSY => NLW_U0_JTAGBUSY_UNCONNECTED,
      JTAGLOCKED => NLW_U0_JTAGLOCKED_UNCONNECTED,
      JTAGMODIFIED => NLW_U0_JTAGMODIFIED_UNCONNECTED,
      MUXADDR(4 downto 0) => NLW_U0_MUXADDR_UNCONNECTED(4 downto 0),
      OT => NLW_U0_OT_UNCONNECTED,
      RESET => reset_in,
      VAUXN(15) => vauxn15,
      VAUXN(14) => '0',
      VAUXN(13) => vauxn13,
      VAUXN(12 downto 10) => B"000",
      VAUXN(9) => vauxn9,
      VAUXN(8 downto 7) => B"00",
      VAUXN(6) => vauxn6,
      VAUXN(5) => vauxn5,
      VAUXN(4 downto 2) => B"000",
      VAUXN(1) => vauxn1,
      VAUXN(0) => '0',
      VAUXP(15) => vauxp15,
      VAUXP(14) => '0',
      VAUXP(13) => vauxp13,
      VAUXP(12 downto 10) => B"000",
      VAUXP(9) => vauxp9,
      VAUXP(8 downto 7) => B"00",
      VAUXP(6) => vauxp6,
      VAUXP(5) => vauxp5,
      VAUXP(4 downto 2) => B"000",
      VAUXP(1) => vauxp1,
      VAUXP(0) => '0',
      VN => vn_in,
      VP => vp_in
    );
end STRUCTURE;
