GMUCERG/fobos/dut/example_cores/AES-128/vhdl/sbox.vhd

--#############################################################################
--#                                                                           #
--#   Copyright 2013-2023 Cryptographic Engineering Research Group (CERG)     #
--#                                                                           #
--#   Licensed under the Apache License, Version 2.0 (the "License");         #
--#   you may not use this file except in compliance with the License.        #
--#   You may obtain a copy of the License at                                 #
--#                                                                           #
--#       http://www.apache.org/licenses/LICENSE-2.0                          #
--#                                                                           #
--#   Unless required by applicable law or agreed to in writing, software     #
--#   distributed under the License is distributed on an "AS IS" BASIS,       #
--#   WITHOUT WARRANTIES OR CONDITIONS OF ANY KIND, either express or implied.#
--#   See the License for the specific language governing permissions and     #
--#   limitations under the License.                                          #
--#                                                                           #
--#############################################################################

----------------------------------------------------------------------------------
-- Company: Cryptographic Engineering Research Group (CERG)
-- ECE Department, George Mason University
--     Fairfax, VA, U.S.A.
--     URL: http://cryptography.gmu.edu
-- Author: Shaunak

library	ieee;
use ieee.std_logic_1164.all;
use	ieee.std_logic_unsigned.all;
use ieee.std_logic_arith.all;

entity sbox is
--generic ( 	bits : integer := 8; -- number of bits per RAM word
--			addr_bits : integer := 7); -- 2^addr_bits = number of words in RAM
port (
		--clock : in std_logic;
		--we : in std_logic;
		a : in std_logic_vector(7 downto 0);
		--di : in std_logic_vector(7 downto 0);
		do : out std_logic_vector(7 downto 0)
	);

end sbox;  

architecture sbox_arch of sbox is										 

type sbox_sub is array (0 to 255) of std_logic_vector (7 downto 0);
signal sbox_value : sbox_sub := ( x"63", x"7c", x"77", x"7b", x"f2", x"6b", x"6f", x"c5", x"30", x"01", x"67", x"2b", x"fe", x"d7", x"ab", x"76",
							  x"ca", x"82", x"c9", x"7d", x"fa", x"59", x"47", x"f0", x"ad", x"d4", x"a2", x"af", x"9c", x"a4", x"72", x"c0",
							  x"b7", x"fd", x"93", x"26", x"36", x"3f", x"f7", x"cc", x"34", x"a5", x"e5", x"f1", x"71", x"d8", x"31", x"15",
							  x"04", x"c7", x"23", x"c3", x"18", x"96", x"05", x"9a", x"07", x"12", x"80", x"e2", x"eb", x"27", x"b2", x"75",
							  x"09", x"83", x"2c", x"1a", x"1b", x"6e", x"5a", x"a0", x"52", x"3b", x"d6", x"b3", x"29", x"e3", x"2f", x"84",
							  x"53", x"d1", x"00", x"ed", x"20", x"fc", x"b1", x"5b", x"6a", x"cb", x"be", x"39", x"4a", x"4c", x"58", x"cf",
							  x"d0", x"ef", x"aa", x"fb", x"43", x"4d", x"33", x"85", x"45", x"f9", x"02", x"7f", x"50", x"3c", x"9f", x"a8",
							  x"51", x"a3", x"40", x"8f", x"92", x"9d", x"38", x"f5", x"bc", x"b6", x"da", x"21", x"10", x"ff", x"f3", x"d2",
							  x"cd", x"0c", x"13", x"ec", x"5f", x"97", x"44", x"17", x"c4", x"a7", x"7e", x"3d", x"64", x"5d", x"19", x"73",
							  x"60", x"81", x"4f", x"dc", x"22", x"2a", x"90", x"88", x"46", x"ee", x"b8", x"14", x"de", x"5e", x"0b", x"db",
							  x"e0", x"32", x"3a", x"0a", x"49", x"06", x"24", x"5c", x"c2", x"d3", x"ac", x"62", x"91", x"95", x"e4", x"79",
							  x"e7", x"c8", x"37", x"6d", x"8d", x"d5", x"4e", x"a9", x"6c", x"56", x"f4", x"ea", x"65", x"7a", x"ae", x"08",
							  x"ba", x"78", x"25", x"2e", x"1c", x"a6", x"b4", x"c6", x"e8", x"dd", x"74", x"1f", x"4b", x"bd", x"8b", x"8a",
							  x"70", x"3e", x"b5", x"66", x"48", x"03", x"f6", x"0e", x"61", x"35", x"57", x"b9", x"86", x"c1", x"1d", x"9e",
							  x"e1", x"f8", x"98", x"11", x"69", x"d9", x"8e", x"94", x"9b", x"1e", x"87", x"e9", x"ce", x"55", x"28", x"df",
							  x"8c", x"a1", x"89", x"0d", x"bf", x"e6", x"42", x"68", x"41", x"99", x"2d", x"0f", x"b0", x"54", x"bb", x"16");

--signal read_a : std_logic_vector(7 downto 0);

begin
--	process (clock)
--		begin
--			if (clock'event and clock = '1') then
--				if (we = '1') then
--					sbox_value(conv_integer(unsigned(a))) <= di;
--				end if;

--				read_a <= a;
				
--			end if;
--	end process;

	do <= sbox_value(conv_integer(unsigned(a)));

end sbox_arch;
